ADBeta/CCCCPPPS/firmware/commands.c

//------------------------------------------------------------------------------
//       Filename: commands.c
//------------------------------------------------------------------------------
//       Ashley Bayliss (c) 2024
//------------------------------------------------------------------------------
//       Purpose : Defines the command parser API
//------------------------------------------------------------------------------
//       Notes : None
//------------------------------------------------------------------------------

//------------------------------------------------------------------------------
// Module includes
//------------------------------------------------------------------------------
#include "commands.h"

//------------------------------------------------------------------------------
// Module constant defines
//------------------------------------------------------------------------------

//------------------------------------------------------------------------------
// External variables
//------------------------------------------------------------------------------

//------------------------------------------------------------------------------
// External functions
//------------------------------------------------------------------------------

//------------------------------------------------------------------------------
// Module type definitions
//------------------------------------------------------------------------------

//------------------------------------------------------------------------------
// Module static variables
//------------------------------------------------------------------------------

//------------------------------------------------------------------------------
// Module static function prototypes
//------------------------------------------------------------------------------

//------------------------------------------------------------------------------
// Module externally exported functions
//------------------------------------------------------------------------------

//------------------------------------------------------------------------------
// Module static functions
//------------------------------------------------------------------------------

//------------------------------------------------------------------------------
//------------------------------------------------------------------------------
//------------------------------------------------------------------------------
