ADBeta/CCCCPPPS/firmware/commands.h

//------------------------------------------------------------------------------
//       Filename: commands.h
//------------------------------------------------------------------------------
//       Ashley Bayliss (c) 2024
//------------------------------------------------------------------------------
//       Purpose : Defines the command parser API
//------------------------------------------------------------------------------
//       Notes : None
//------------------------------------------------------------------------------
#pragma once

#ifdef __cplusplus
extern "C" {
#endif

//------------------------------------------------------------------------------
// Module includes
//------------------------------------------------------------------------------

//------------------------------------------------------------------------------
// Module exported defines
//------------------------------------------------------------------------------

//------------------------------------------------------------------------------
// Module exported type definitions
//------------------------------------------------------------------------------

//------------------------------------------------------------------------------
// Module exported functions
//------------------------------------------------------------------------------

//------------------------------------------------------------------------------
// Module exported variables
//------------------------------------------------------------------------------

//------------------------------------------------------------------------------
//------------------------------------------------------------------------------
//------------------------------------------------------------------------------

#ifdef __cplusplus
}
#endif
